elfren/SharpeningJigs/Pucks/Drill/3-16/Drill_Puck_60V_35R_3-16.stl

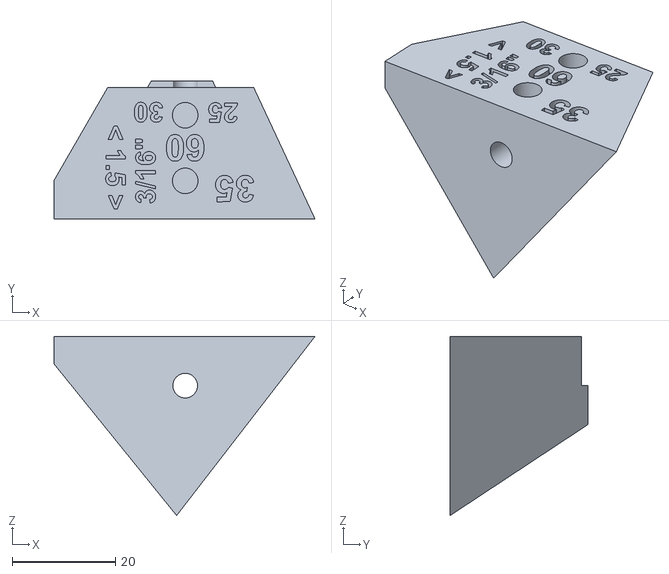
[picture p14: CAD file, 2022-11-19]
Pucks/Drill/3-16/Drill_Puck_60V_35R_3-16.stl
50.5 x 26.7 x 34.7
