elfren/SharpeningJigs/Pucks/Drill/6mm/Drill_Puck_135V_35R_6mm.stl

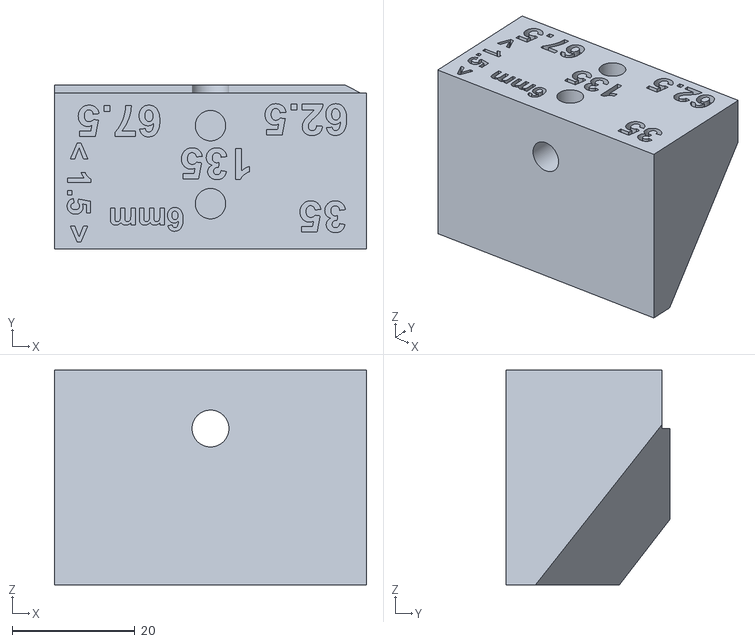
[picture p15: CAD file, 2022-11-19]
Pucks/Drill/6mm/Drill_Puck_135V_35R_6mm.stl
50.8 x 26.7 x 35.0
