elfren/SharpeningJigs/Pucks/FlyCutter/3-16/FlyCutter_Puck_90V_35R_3-16.stl

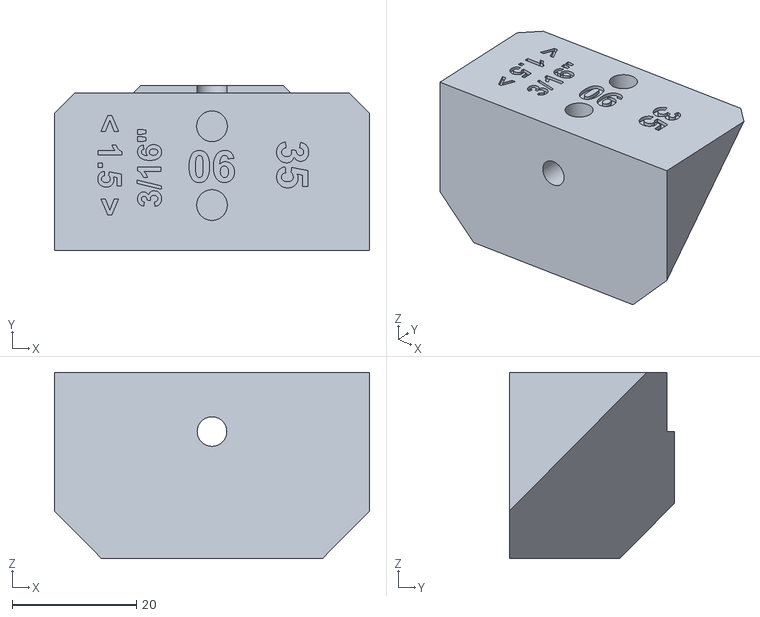
[picture p16: CAD file, 2022-11-19]
Pucks/FlyCutter/3-16/FlyCutter_Puck_90V_35R_3-16.stl
50.8 x 26.7 x 30.0
