elfren/SharpeningJigs/Pucks/Drill/1-8/Drill_Puck_75V_35R_1-8.stl

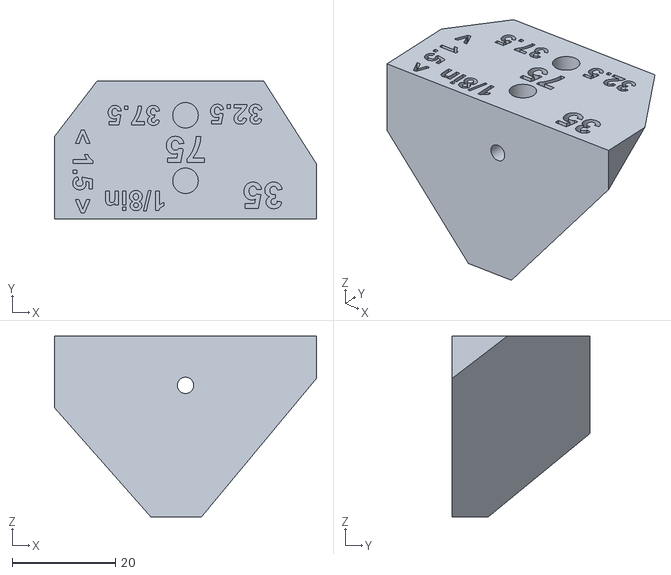
[picture p18: CAD file, 2022-11-19]
Pucks/Drill/1-8/Drill_Puck_75V_35R_1-8.stl
50.8 x 26.7 x 35.0
