elfren/SharpeningJigs/Pucks/Drill/3-16/Drill_Puck_90V_35R_3-16.stl

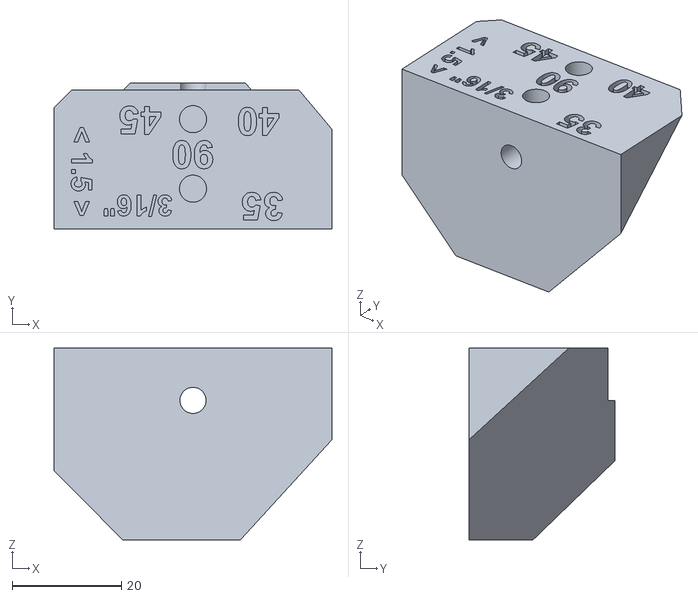
[picture p22: CAD file, 2022-11-19]
Pucks/Drill/3-16/Drill_Puck_90V_35R_3-16.stl
50.8 x 26.7 x 35.0
