elfren/SharpeningJigs/Pucks/FlyCutter/6mm/FlyCutter_Puck_105V_35R_6mm.stl

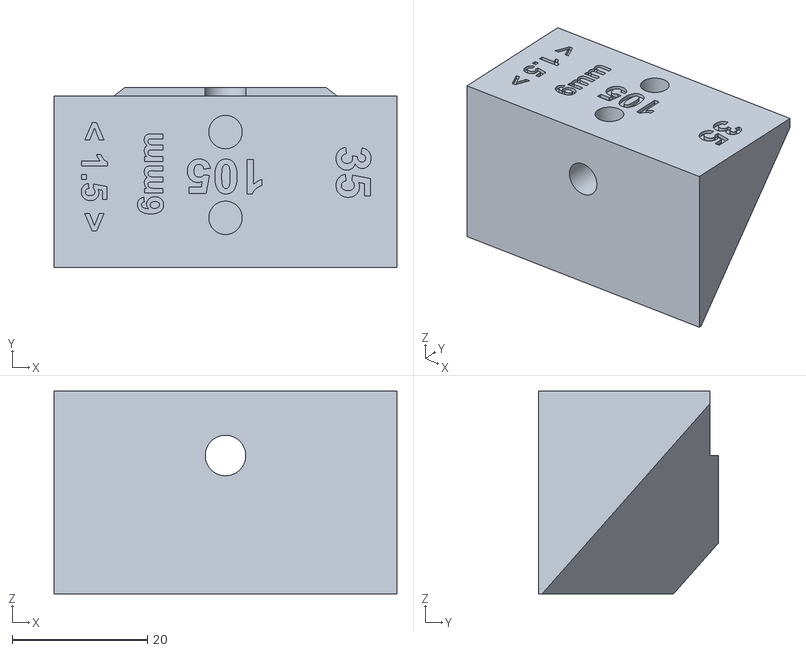
[picture p25: CAD file, 2022-11-19]
Pucks/FlyCutter/6mm/FlyCutter_Puck_105V_35R_6mm.stl
50.8 x 26.7 x 30.0
