elfren/SharpeningJigs/Pucks/FlyCutter/1-8/FlyCutter_Puck_75V_35R_1-8.stl

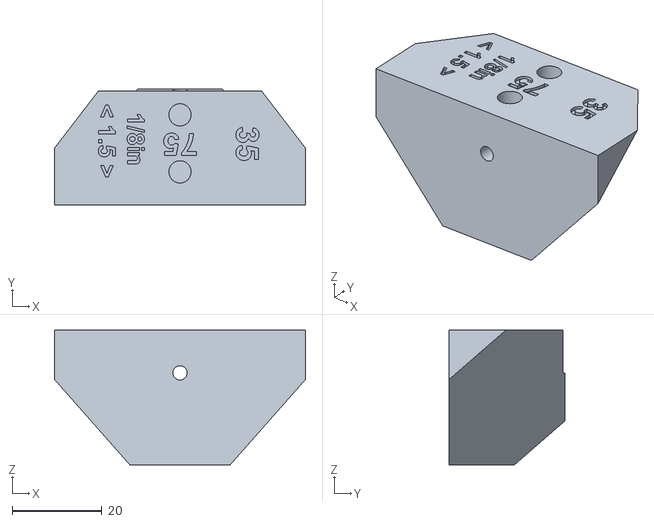
[picture p27: CAD file, 2022-11-19]
Pucks/FlyCutter/1-8/FlyCutter_Puck_75V_35R_1-8.stl
55.9 x 25.8 x 30.0
