elfren/SharpeningJigs/Pucks/Drill/1-8/Drill_Puck_60V_35R_1-8.stl

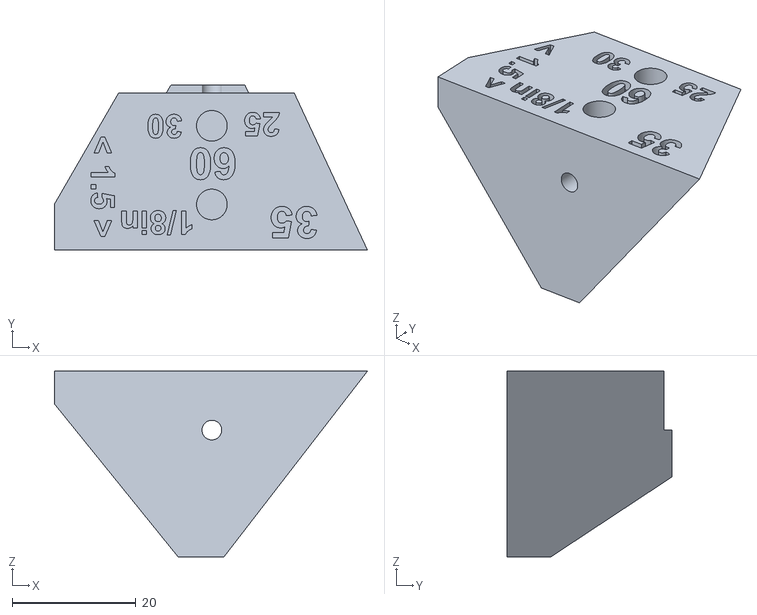
[picture p28: CAD file, 2022-11-19]
Pucks/Drill/1-8/Drill_Puck_60V_35R_1-8.stl
50.5 x 26.7 x 30.0
