elfren/SharpeningJigs/Pucks/FlyCutter/1-8/FlyCutter_Puck_135V_35R_1-8.stl

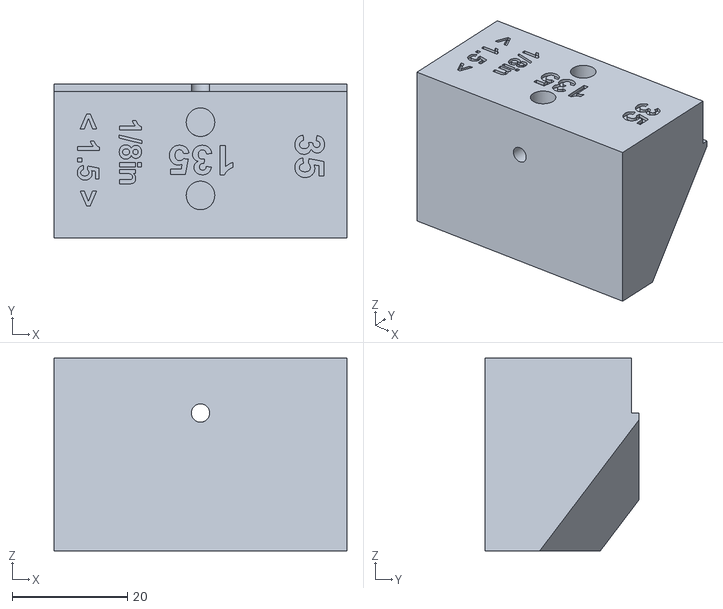
[picture p29: CAD file, 2022-11-19]
Pucks/FlyCutter/1-8/FlyCutter_Puck_135V_35R_1-8.stl
50.8 x 26.7 x 33.4
